AlexiaRat/E-Reader/Images/Baterie.png

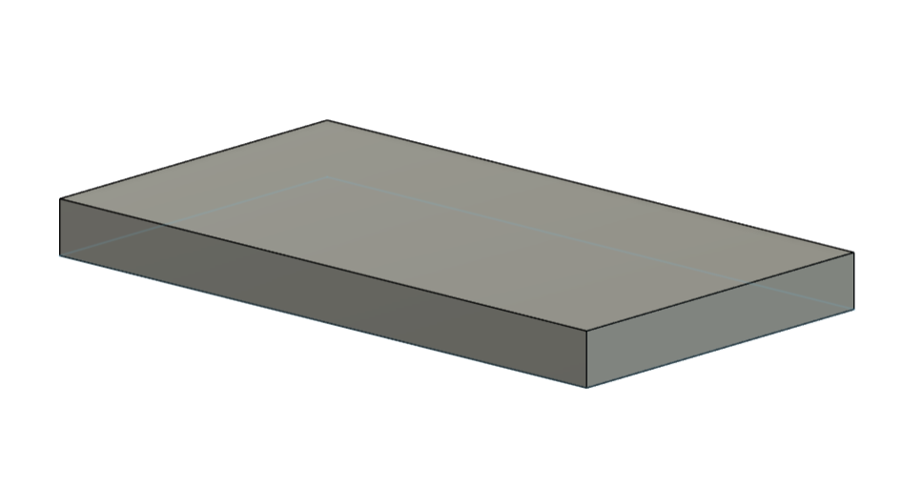
Images/Baterie.png
